himikat123/Weather-Monitor-BIM/Enclosure/solidworks2023/buttons/settings_button.png

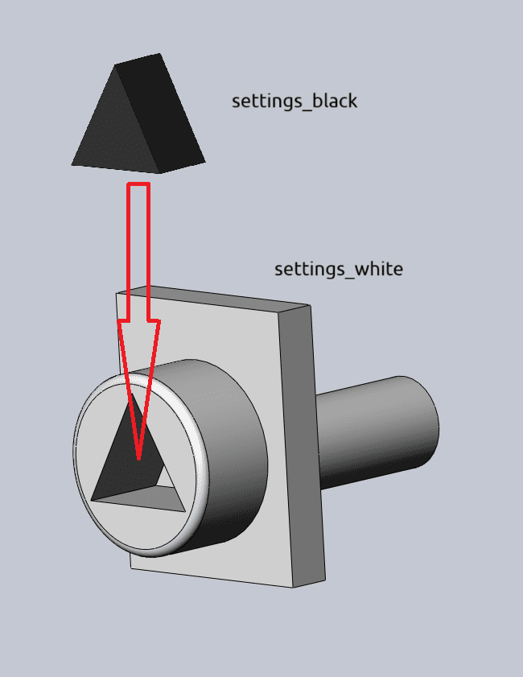
Enclosure/solidworks2023/buttons/settings_button.png
