himikat123/Weather-Monitor-BIM/Enclosure/solidworks2023/cover/cover.png

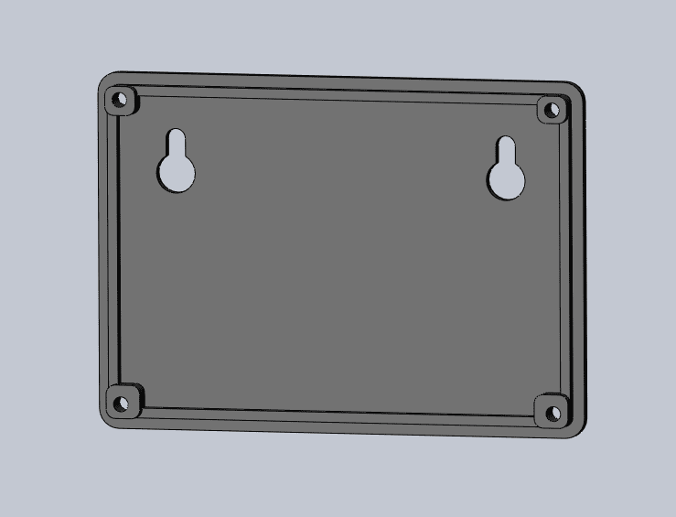
Enclosure/solidworks2023/cover/cover.png
