himikat123/Weather-Monitor-BIM/Enclosure/solidworks2023/face/face.png

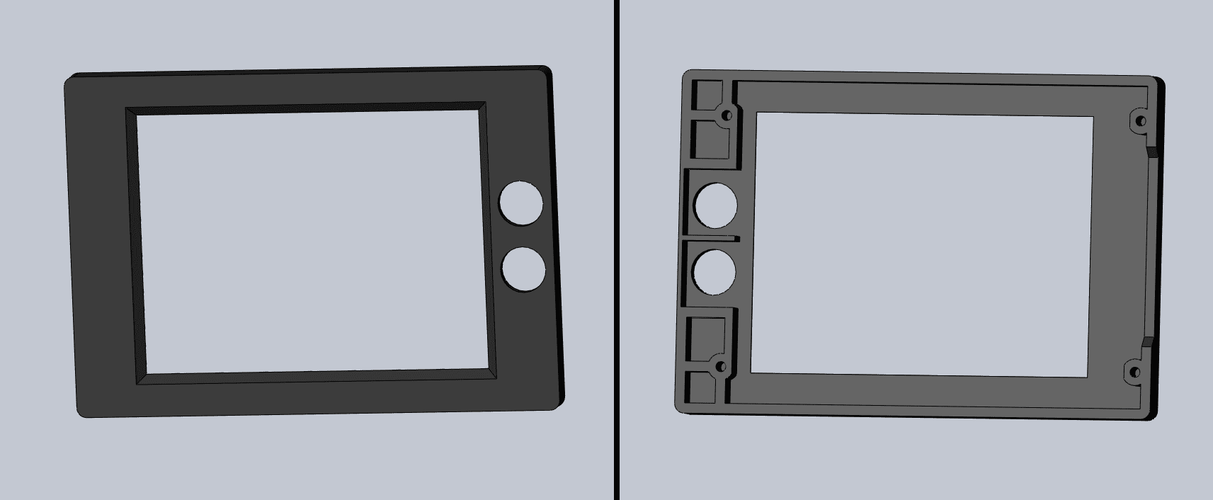
Enclosure/solidworks2023/face/face.png
