himikat123/Weather-Monitor-BIM/Enclosure/solidworks2023/frame/frame.png

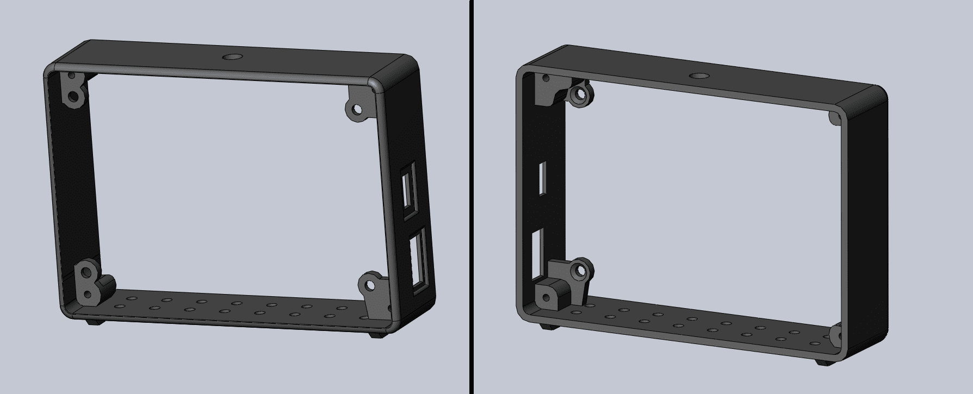
Enclosure/solidworks2023/frame/frame.png
