himikat123/Weather-Monitor-BIM/Enclosure/solidworks2023/pcb/PCB.png

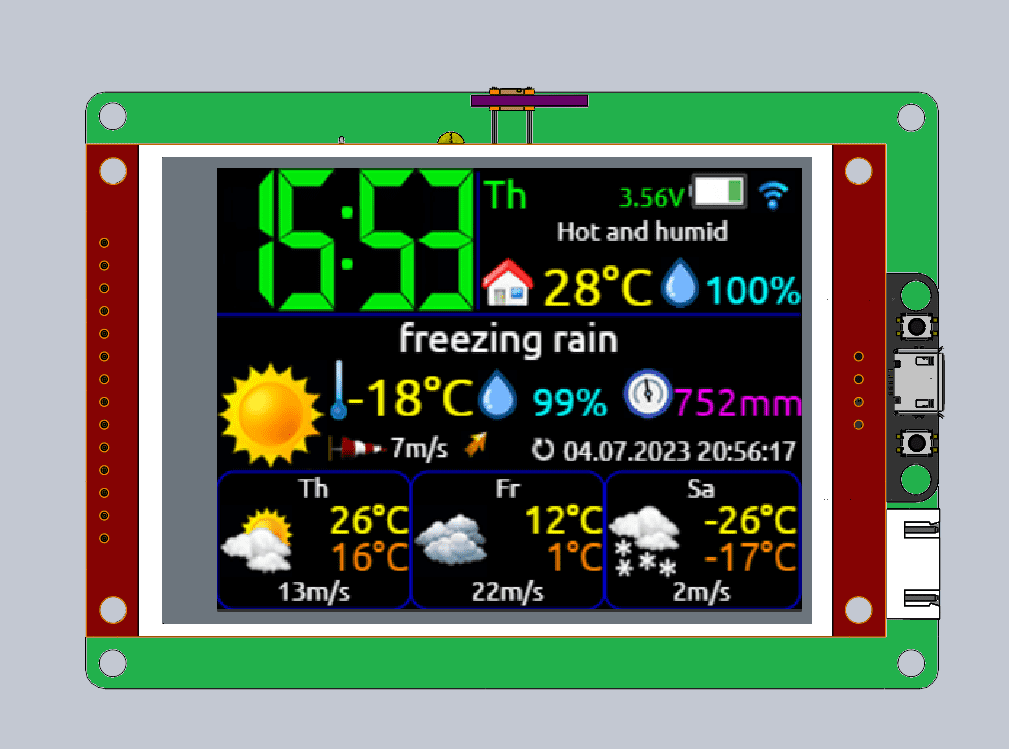
Enclosure/solidworks2023/pcb/PCB.png
