himikat123/Weather-Monitor-BIM/Enclosure/STL/buttons.jpg

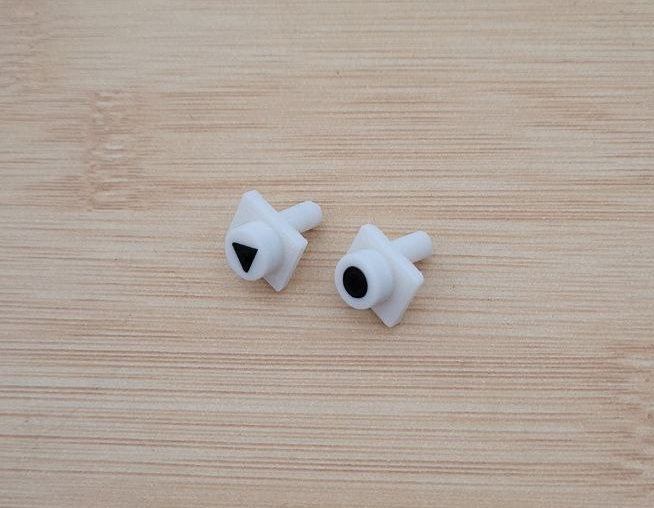
Enclosure/STL/buttons.jpg
