himikat123/Weather-Monitor-BIM/Enclosure/STL/buttons/one_color/reset.png

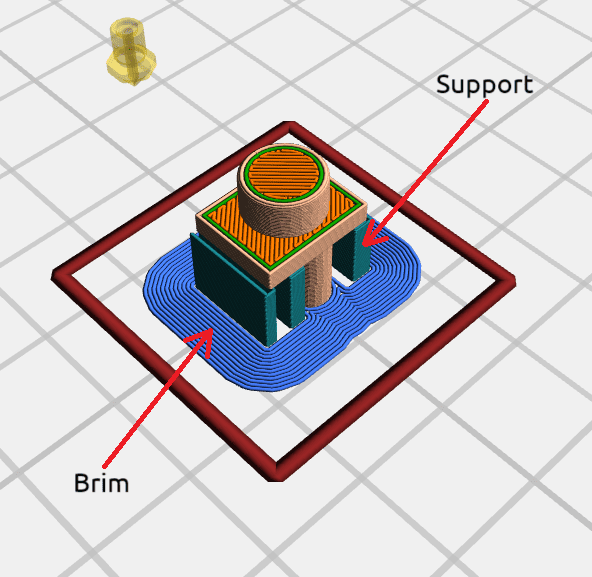
Enclosure/STL/buttons/one_color/reset.png
