himikat123/Weather-Monitor-BIM/Enclosure/STL/buttons/one_color/settings.png

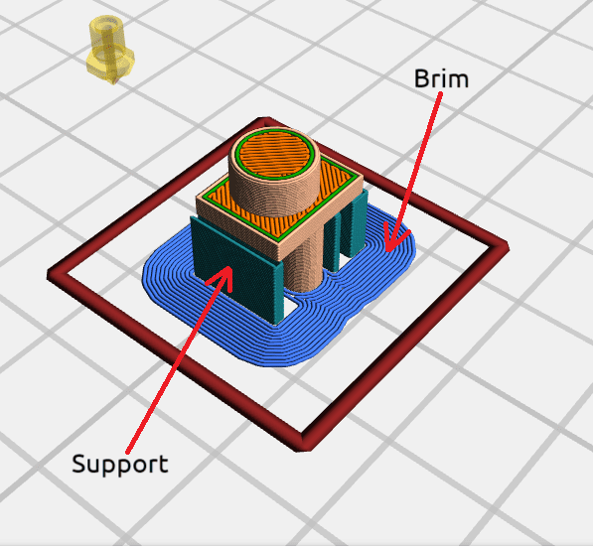
Enclosure/STL/buttons/one_color/settings.png
