himikat123/Weather-Monitor-BIM/Enclosure/STL/buttons/two_colors/reset_white.png

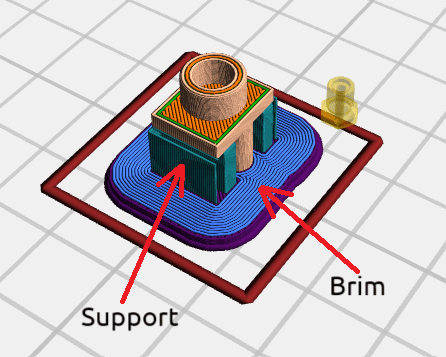
Enclosure/STL/buttons/two_colors/reset_white.png
