himikat123/Weather-Monitor-BIM/Enclosure/STL/buttons/two_colors/settings_black.png

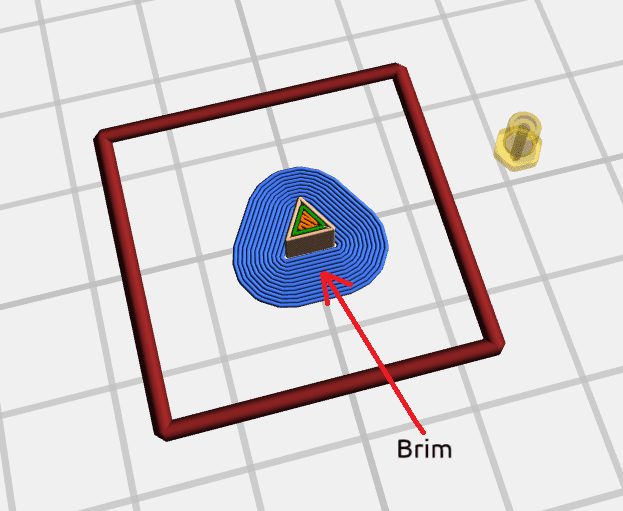
Enclosure/STL/buttons/two_colors/settings_black.png
