himikat123/Weather-Monitor-BIM/Enclosure/STL/cover/cover.png

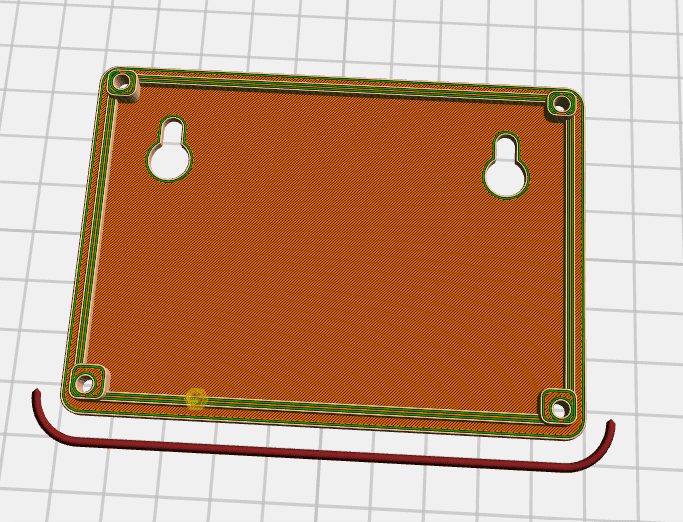
Enclosure/STL/cover/cover.png
