himikat123/Weather-Monitor-BIM/Enclosure/STL/face.jpg

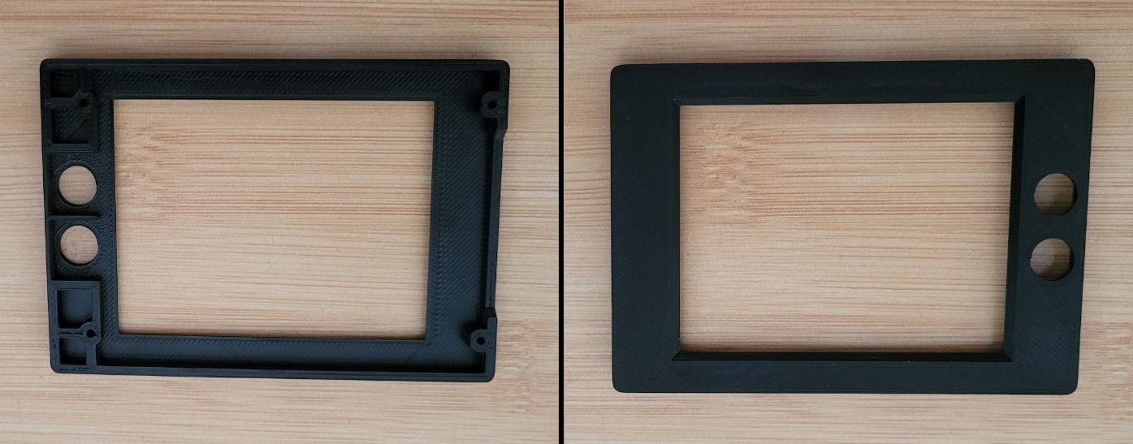
Enclosure/STL/face.jpg
