himikat123/Weather-Monitor-BIM/Enclosure/STL/face/face.png

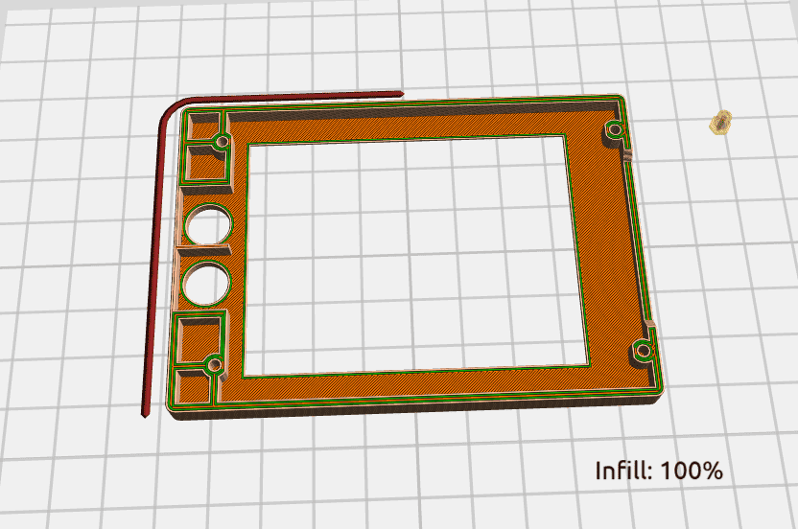
Enclosure/STL/face/face.png
