himikat123/Weather-Monitor-BIM/Enclosure/STL/face/face_wo_button_holes.png

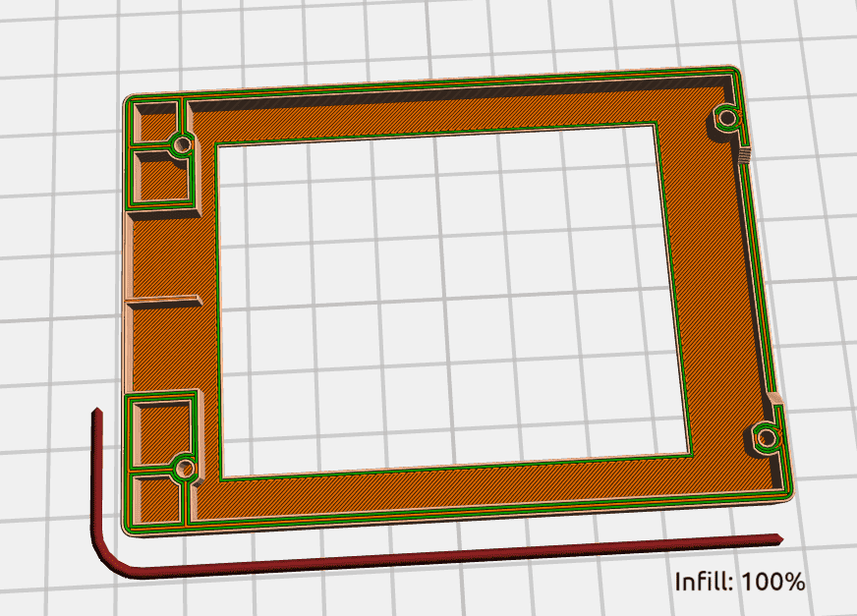
Enclosure/STL/face/face_wo_button_holes.png
