himikat123/Weather-Monitor-BIM/Enclosure/STL/frame.jpg

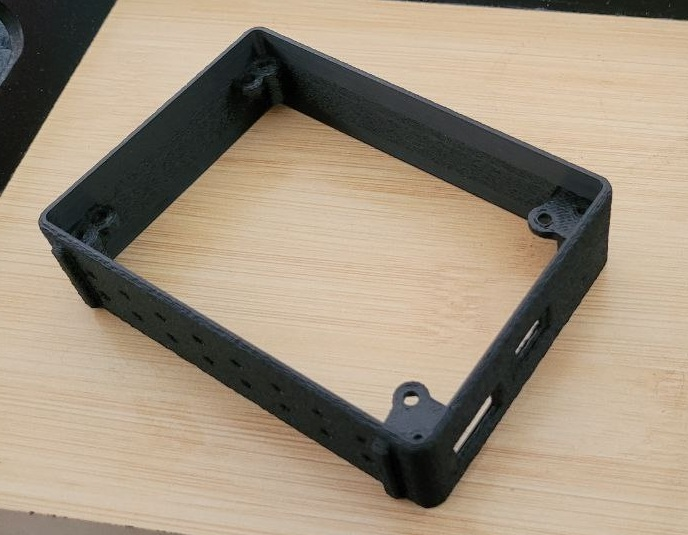
Enclosure/STL/frame.jpg
