himikat123/Weather-Monitor-BIM/Enclosure/STL/frame/frame.png

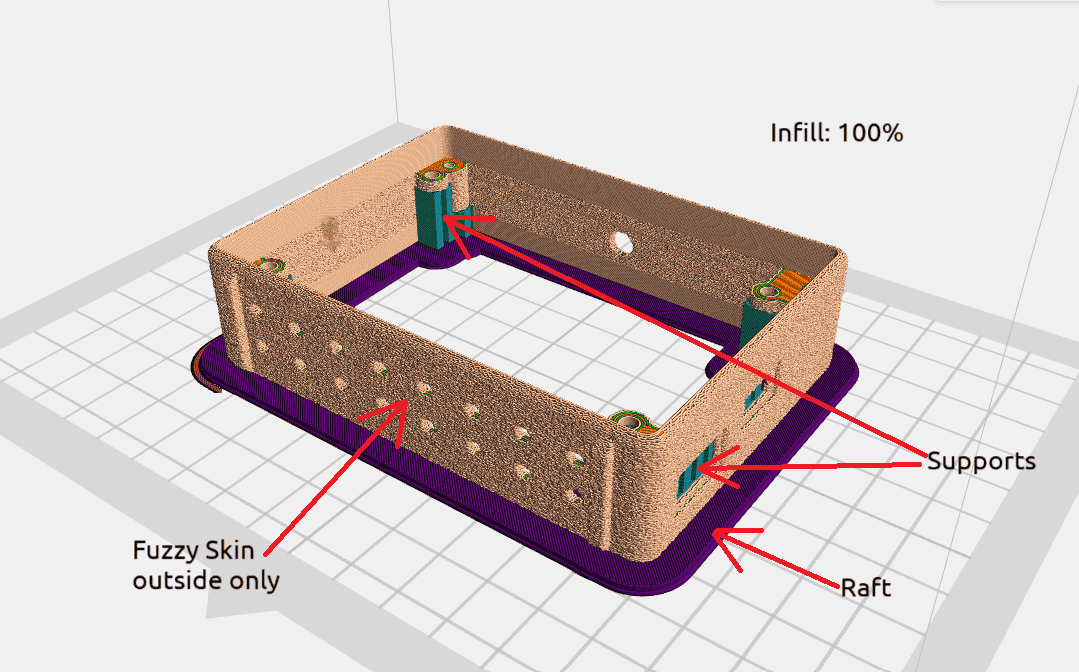
Enclosure/STL/frame/frame.png
