himikat123/Weather-Monitor-BIM/Enclosure/STL/frame/frame_wo_extra_holes.png

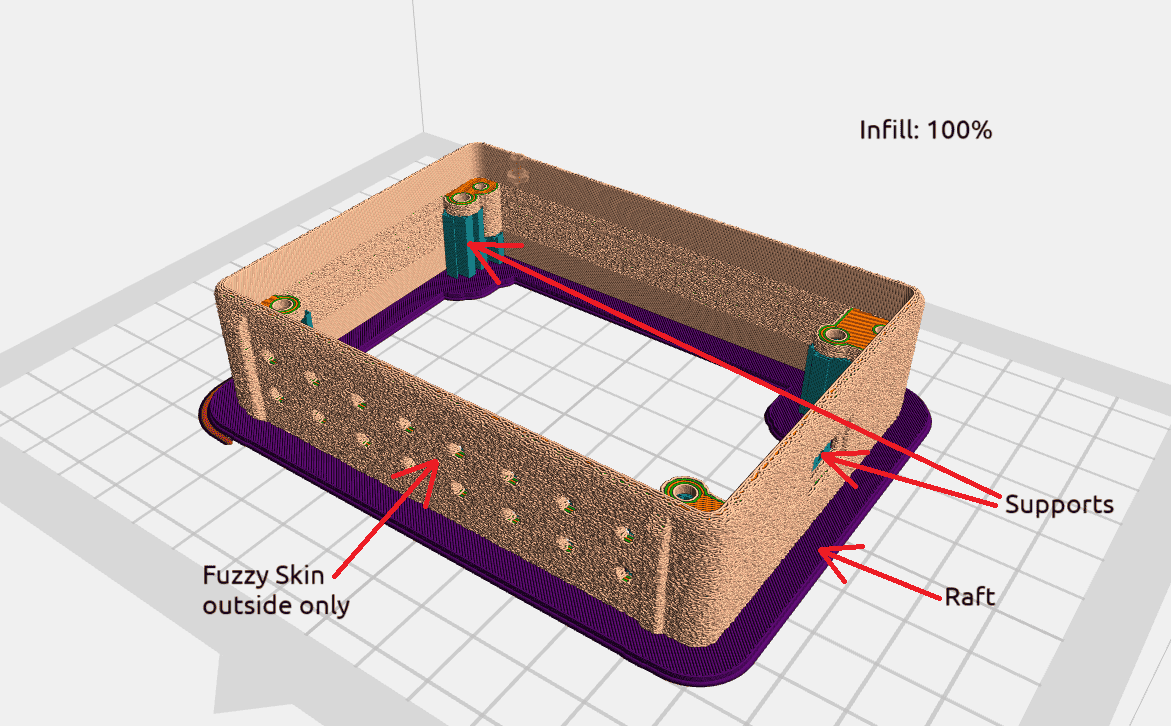
Enclosure/STL/frame/frame_wo_extra_holes.png
