himikat123/Weather-Monitor-BIM/Enclosure/STL/frame/frame_wo_light_sensor_hole.png

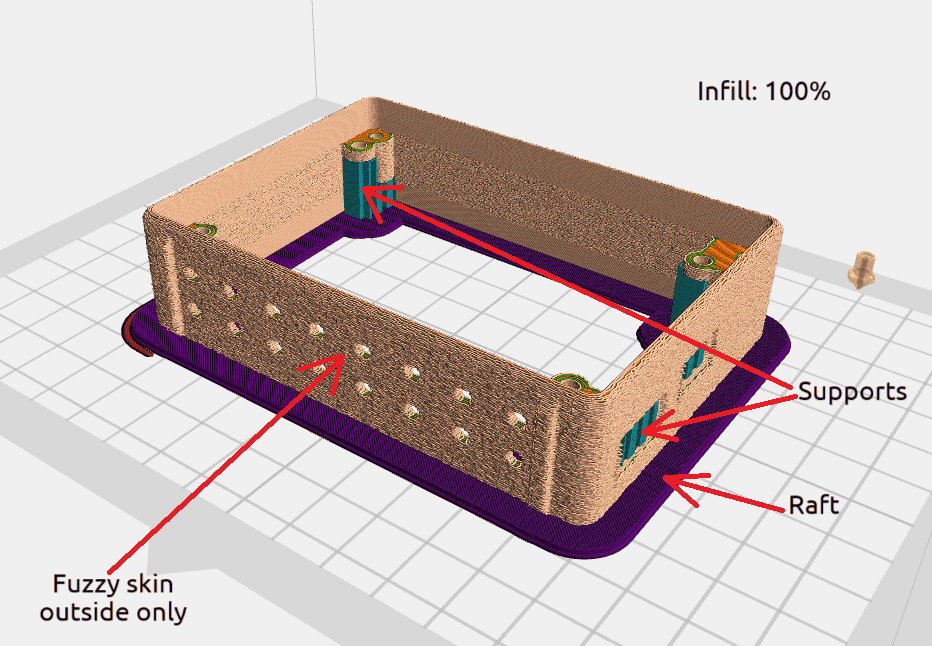
Enclosure/STL/frame/frame_wo_light_sensor_hole.png
