himikat123/Weather-Monitor-BIM/Enclosure/STL/frame/frame_wo_sensors_connector_hole.png

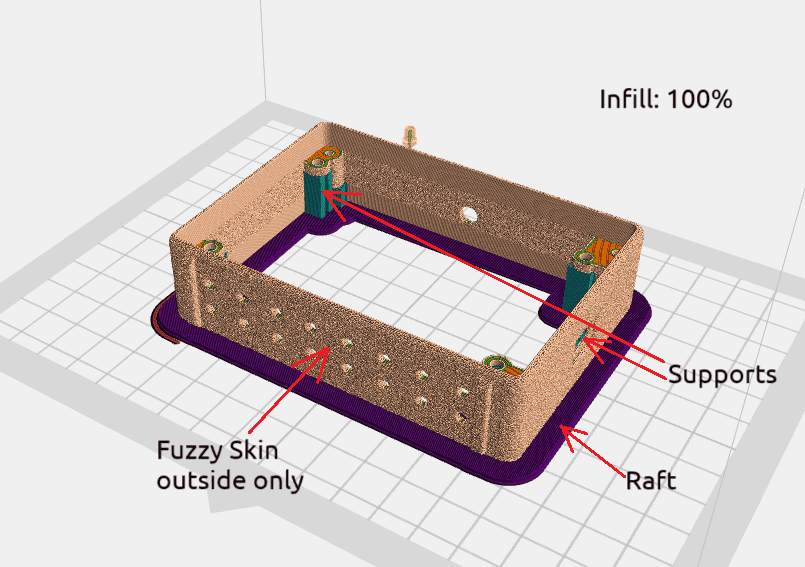
Enclosure/STL/frame/frame_wo_sensors_connector_hole.png
