himikat123/Weather-Monitor-BIM/Enclosure/STL/screws.jpg

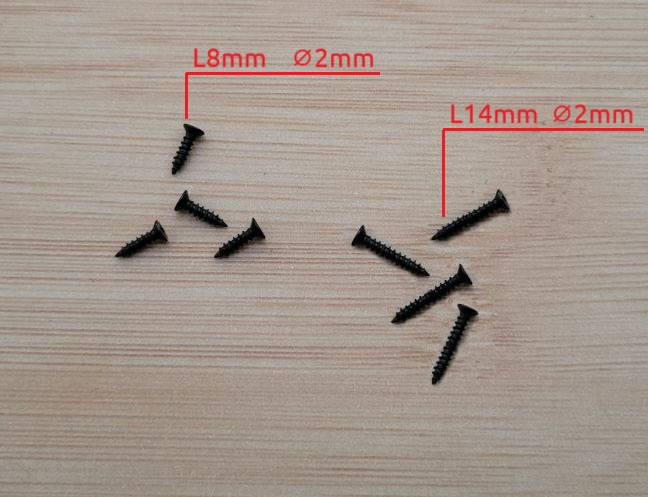
Enclosure/STL/screws.jpg
