himikat123/Weather-Monitor-BIM/img/bme280.png

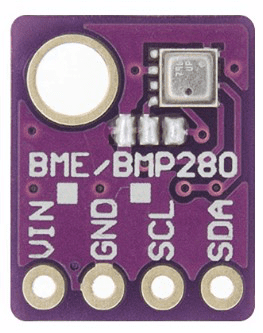
img/bme280.png
