himikat123/Weather-Monitor-BIM/img/bmp180.png

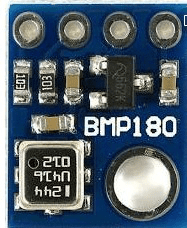
img/bmp180.png
