himikat123/Weather-Monitor-BIM/img/ili9341.png

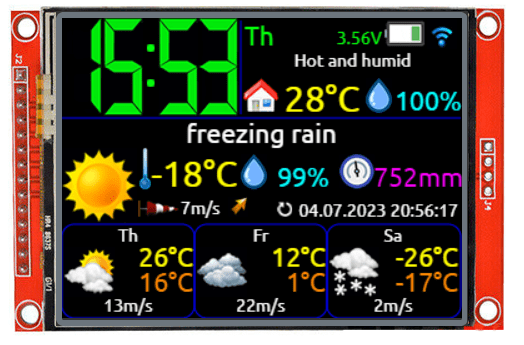
img/ili9341.png
