himikat123/Weather-Monitor-BIM/img/main_RU.png

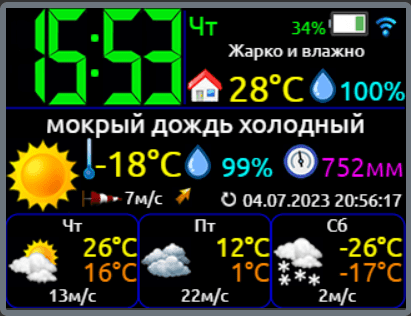
img/main_RU.png
