himikat123/Weather-Monitor-BIM/img/max44009.png

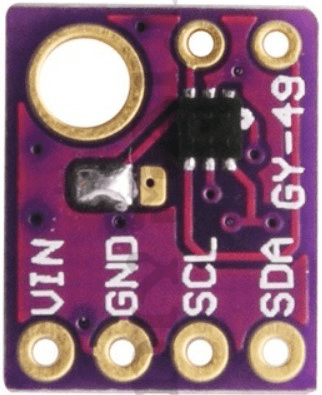
img/max44009.png
