himikat123/Weather-Monitor-BIM/PCB/BIM.png

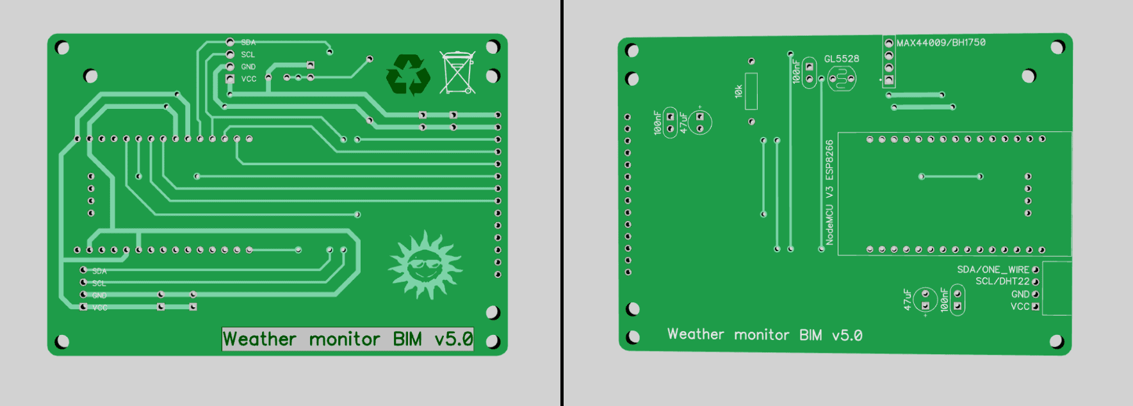
PCB/BIM.png
