himikat123/Weather-Monitor-BIM/PCB/DipTrace4.2.0.1/3d models/JST - XH - Thru (R) - 4Pin - 2.54mm.stp

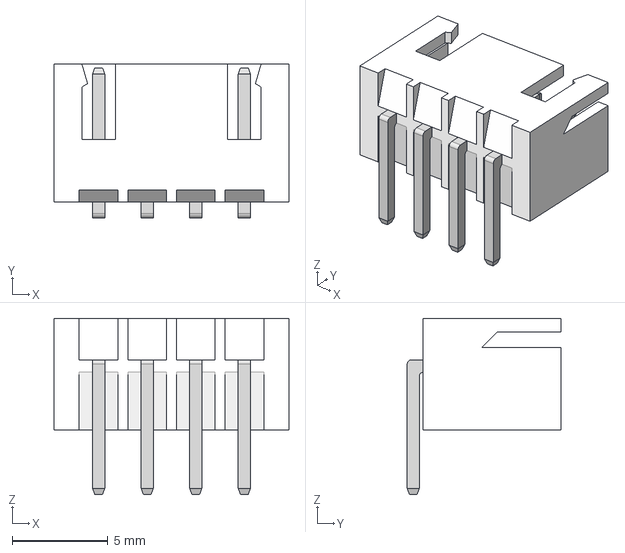
[picture p57: CAD file, 2024-08-09]
PCB/DipTrace4.2.0.1/3d models/JST - XH - Thru (R) - 4Pin - 2.54mm.stp
12.3 x 8.04 x 9.22 mm
