himikat123/Weather-Monitor-BIM/Enclosure/solidworks2023/buttons/settings_black.SLDPRT

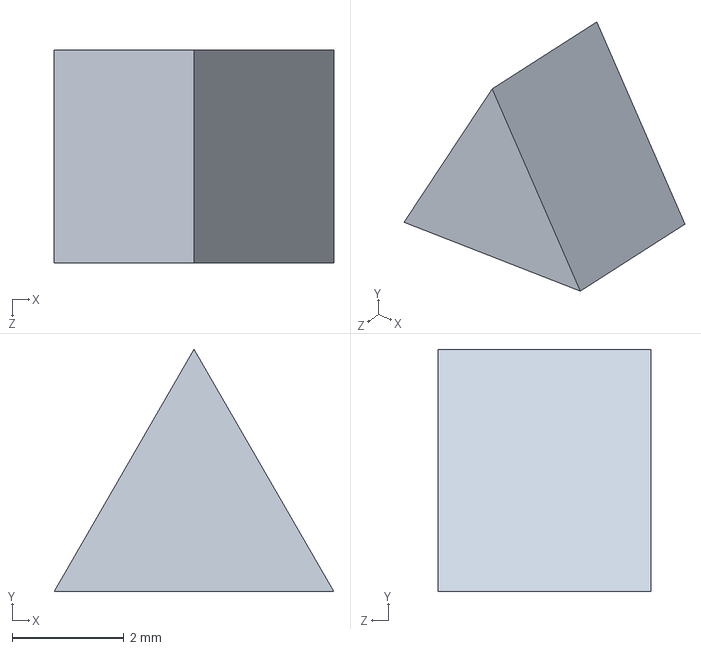
[picture p58: CAD file, 2024-10-13]
Enclosure/solidworks2023/buttons/settings_black.SLDPRT
5.00 x 4.33 x 3.80 mm
