himikat123/Weather-Monitor-BIM/Enclosure/solidworks2023/pcb/touch.SLDPRT

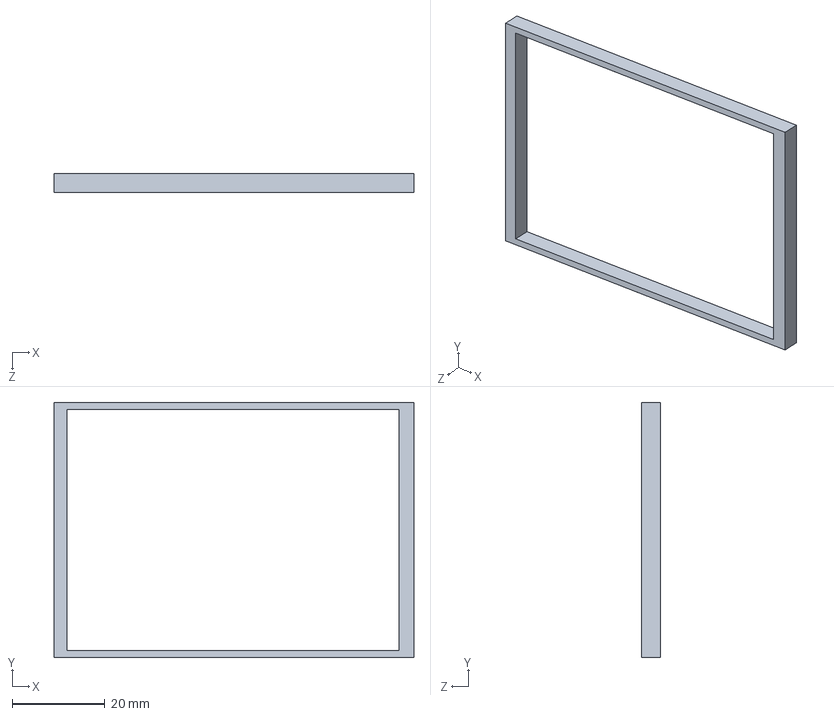
[picture p59: CAD file, 2024-08-09]
Enclosure/solidworks2023/pcb/touch.SLDPRT
77.6 x 55.0 x 4.00 mm
