himikat123/Weather-Monitor-BIM/Enclosure/STL/buttons/two_colors/reset_black.STL

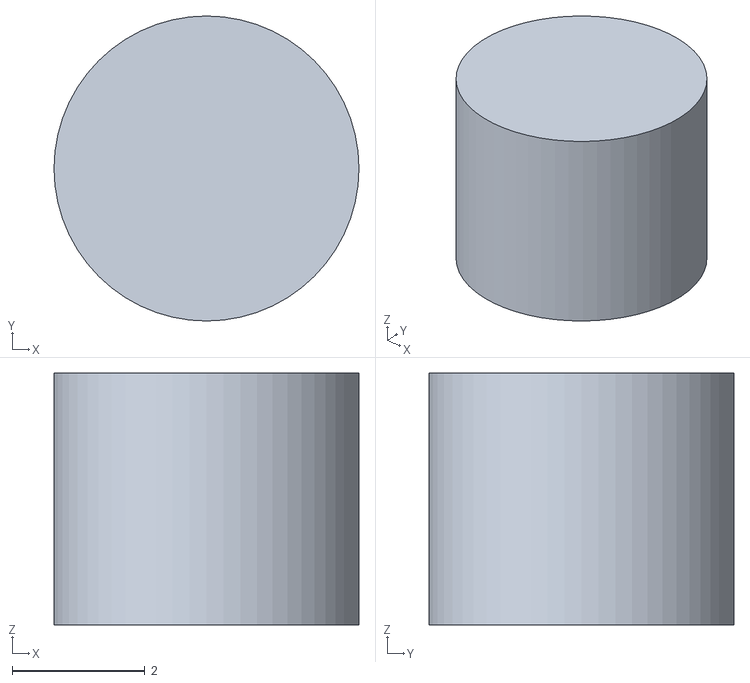
[picture p60: CAD file, 2024-10-13]
Enclosure/STL/buttons/two_colors/reset_black.STL
4.60 x 4.60 x 3.80
