himikat123/Weather-Monitor-BIM/PCB/DipTrace4.2.0.1/3d models/ESP8266.stp

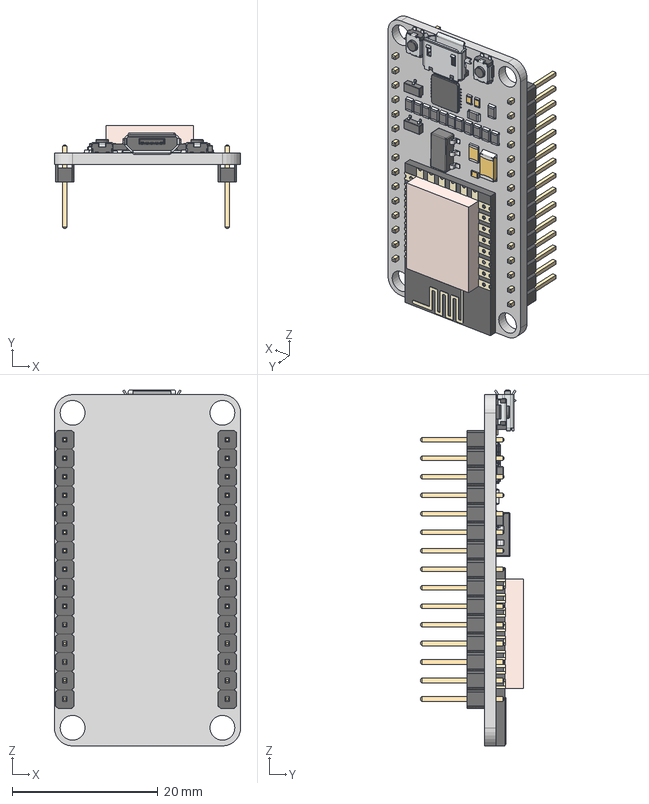
[picture p61: CAD file, 2024-08-09]
PCB/DipTrace4.2.0.1/3d models/ESP8266.stp
25.6 x 14.1 x 48.8 mm
micro usb shell
micro usb internal
micro usb contact x 5
switch v1
switch v1 (1)
spacer x 15
pin x 15
spacer (1) (1) x 15
pin (1) (1) x 15
TSOP-5 v4 v1
TSOP-5 v4 v1 (1)
TSOP-5 v4 v1 (1) (1)
R0805-NO v1 x 13
R0805-NO v1 (1) x 2
R0805-NO v1 (1) (1)
R0805-NO v1 (1) (2)
R0805-NO v1 (1) (3)
Cuerpo Microprocesador v1
