himikat123/Weather-Monitor-BIM/Enclosure/solidworks2023/pcb/board.SLDPRT

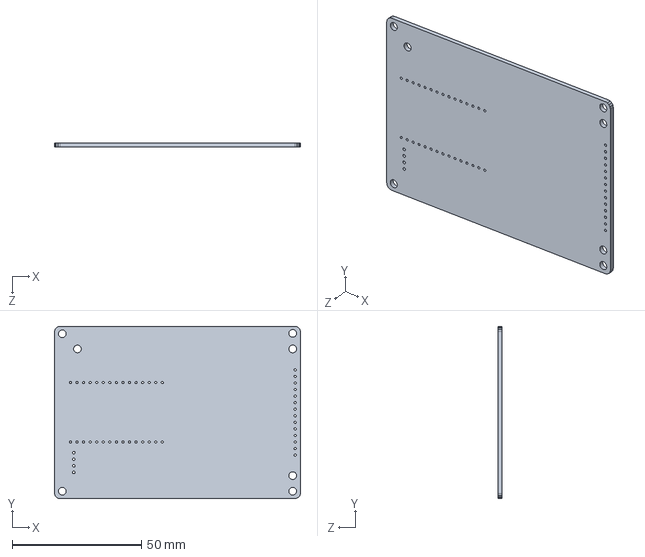
[picture p62: CAD file, 2024-08-09]
Enclosure/solidworks2023/pcb/board.SLDPRT
95.2 x 66.7 x 1.59 mm
