himikat123/Weather-Monitor-BIM/PCB/DipTrace4.2.0.1/3d models/ILI9341_3_2.step

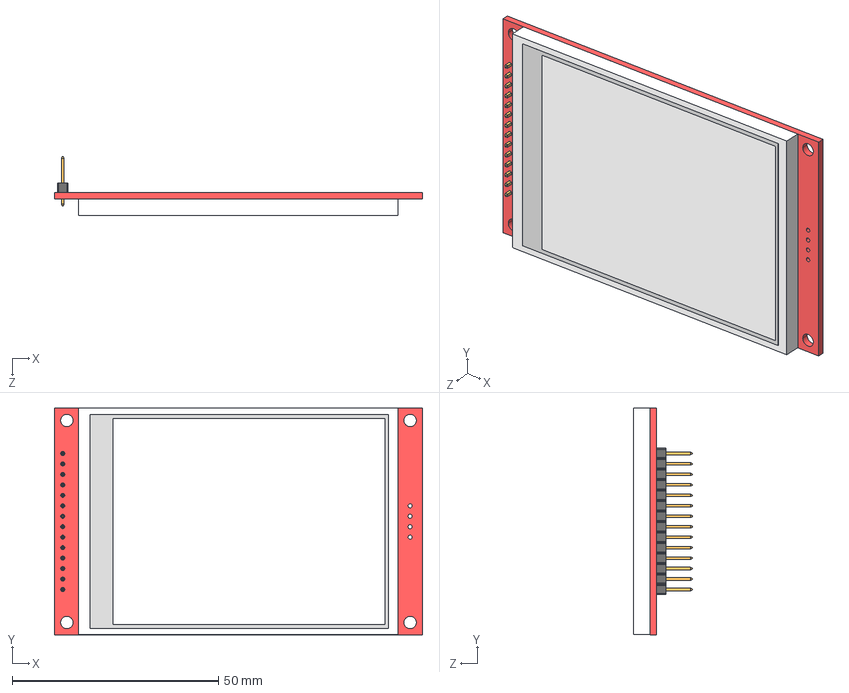
[picture p63: CAD file, 2024-08-09]
PCB/DipTrace4.2.0.1/3d models/ILI9341_3_2.step
89.3 x 55.0 x 14.2 mm
screen
disp_frame
touch
display_board
14-Pin Header - Male - 2.54mm_1.step
