himikat123/Weather-Monitor-BIM/PCB/DipTrace4.2.0.1/3d models/1x9.STEP

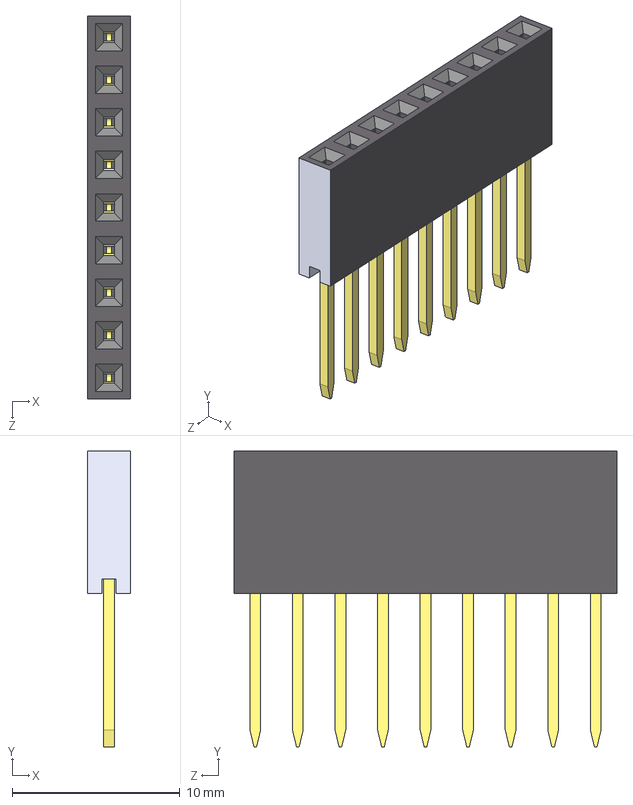
[picture p64: CAD file, 2024-08-09]
PCB/DipTrace4.2.0.1/3d models/1x9.STEP
2.54 x 17.6 x 22.9 mm
