himikat123/Weather-Monitor-BIM/Enclosure/solidworks2023/pcb/screen.SLDPRT

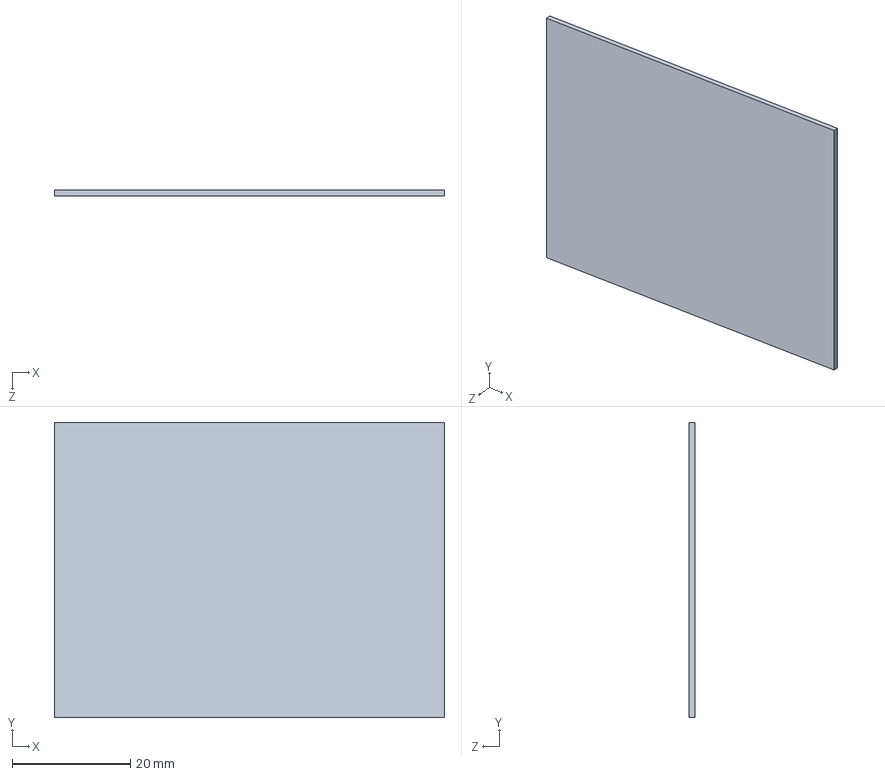
[picture p65: CAD file, 2024-08-09]
Enclosure/solidworks2023/pcb/screen.SLDPRT
66.0 x 50.0 x 1.00 mm
