himikat123/Weather-Monitor-BIM/PCB/DipTrace4.2.0.1/3d models/GL5528.stp

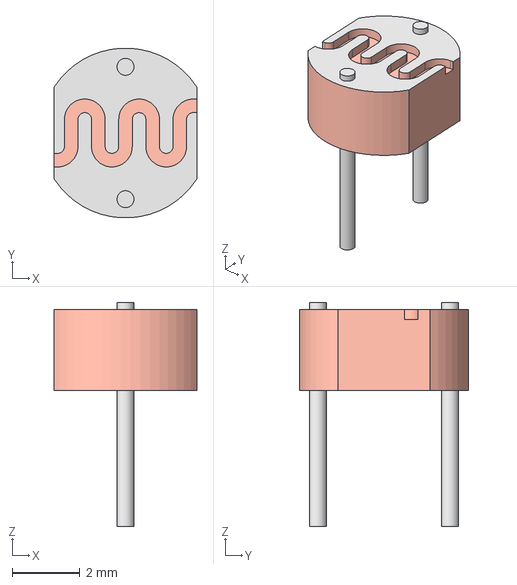
[picture p66: CAD file, 2024-08-09]
PCB/DipTrace4.2.0.1/3d models/GL5528.stp
4.20 x 4.99 x 6.60 mm
